episource/picopdio/schematics/picopdio.kicad_sch

## KiCad design schematics/picopdio.kicad_sch (2023-12-19)

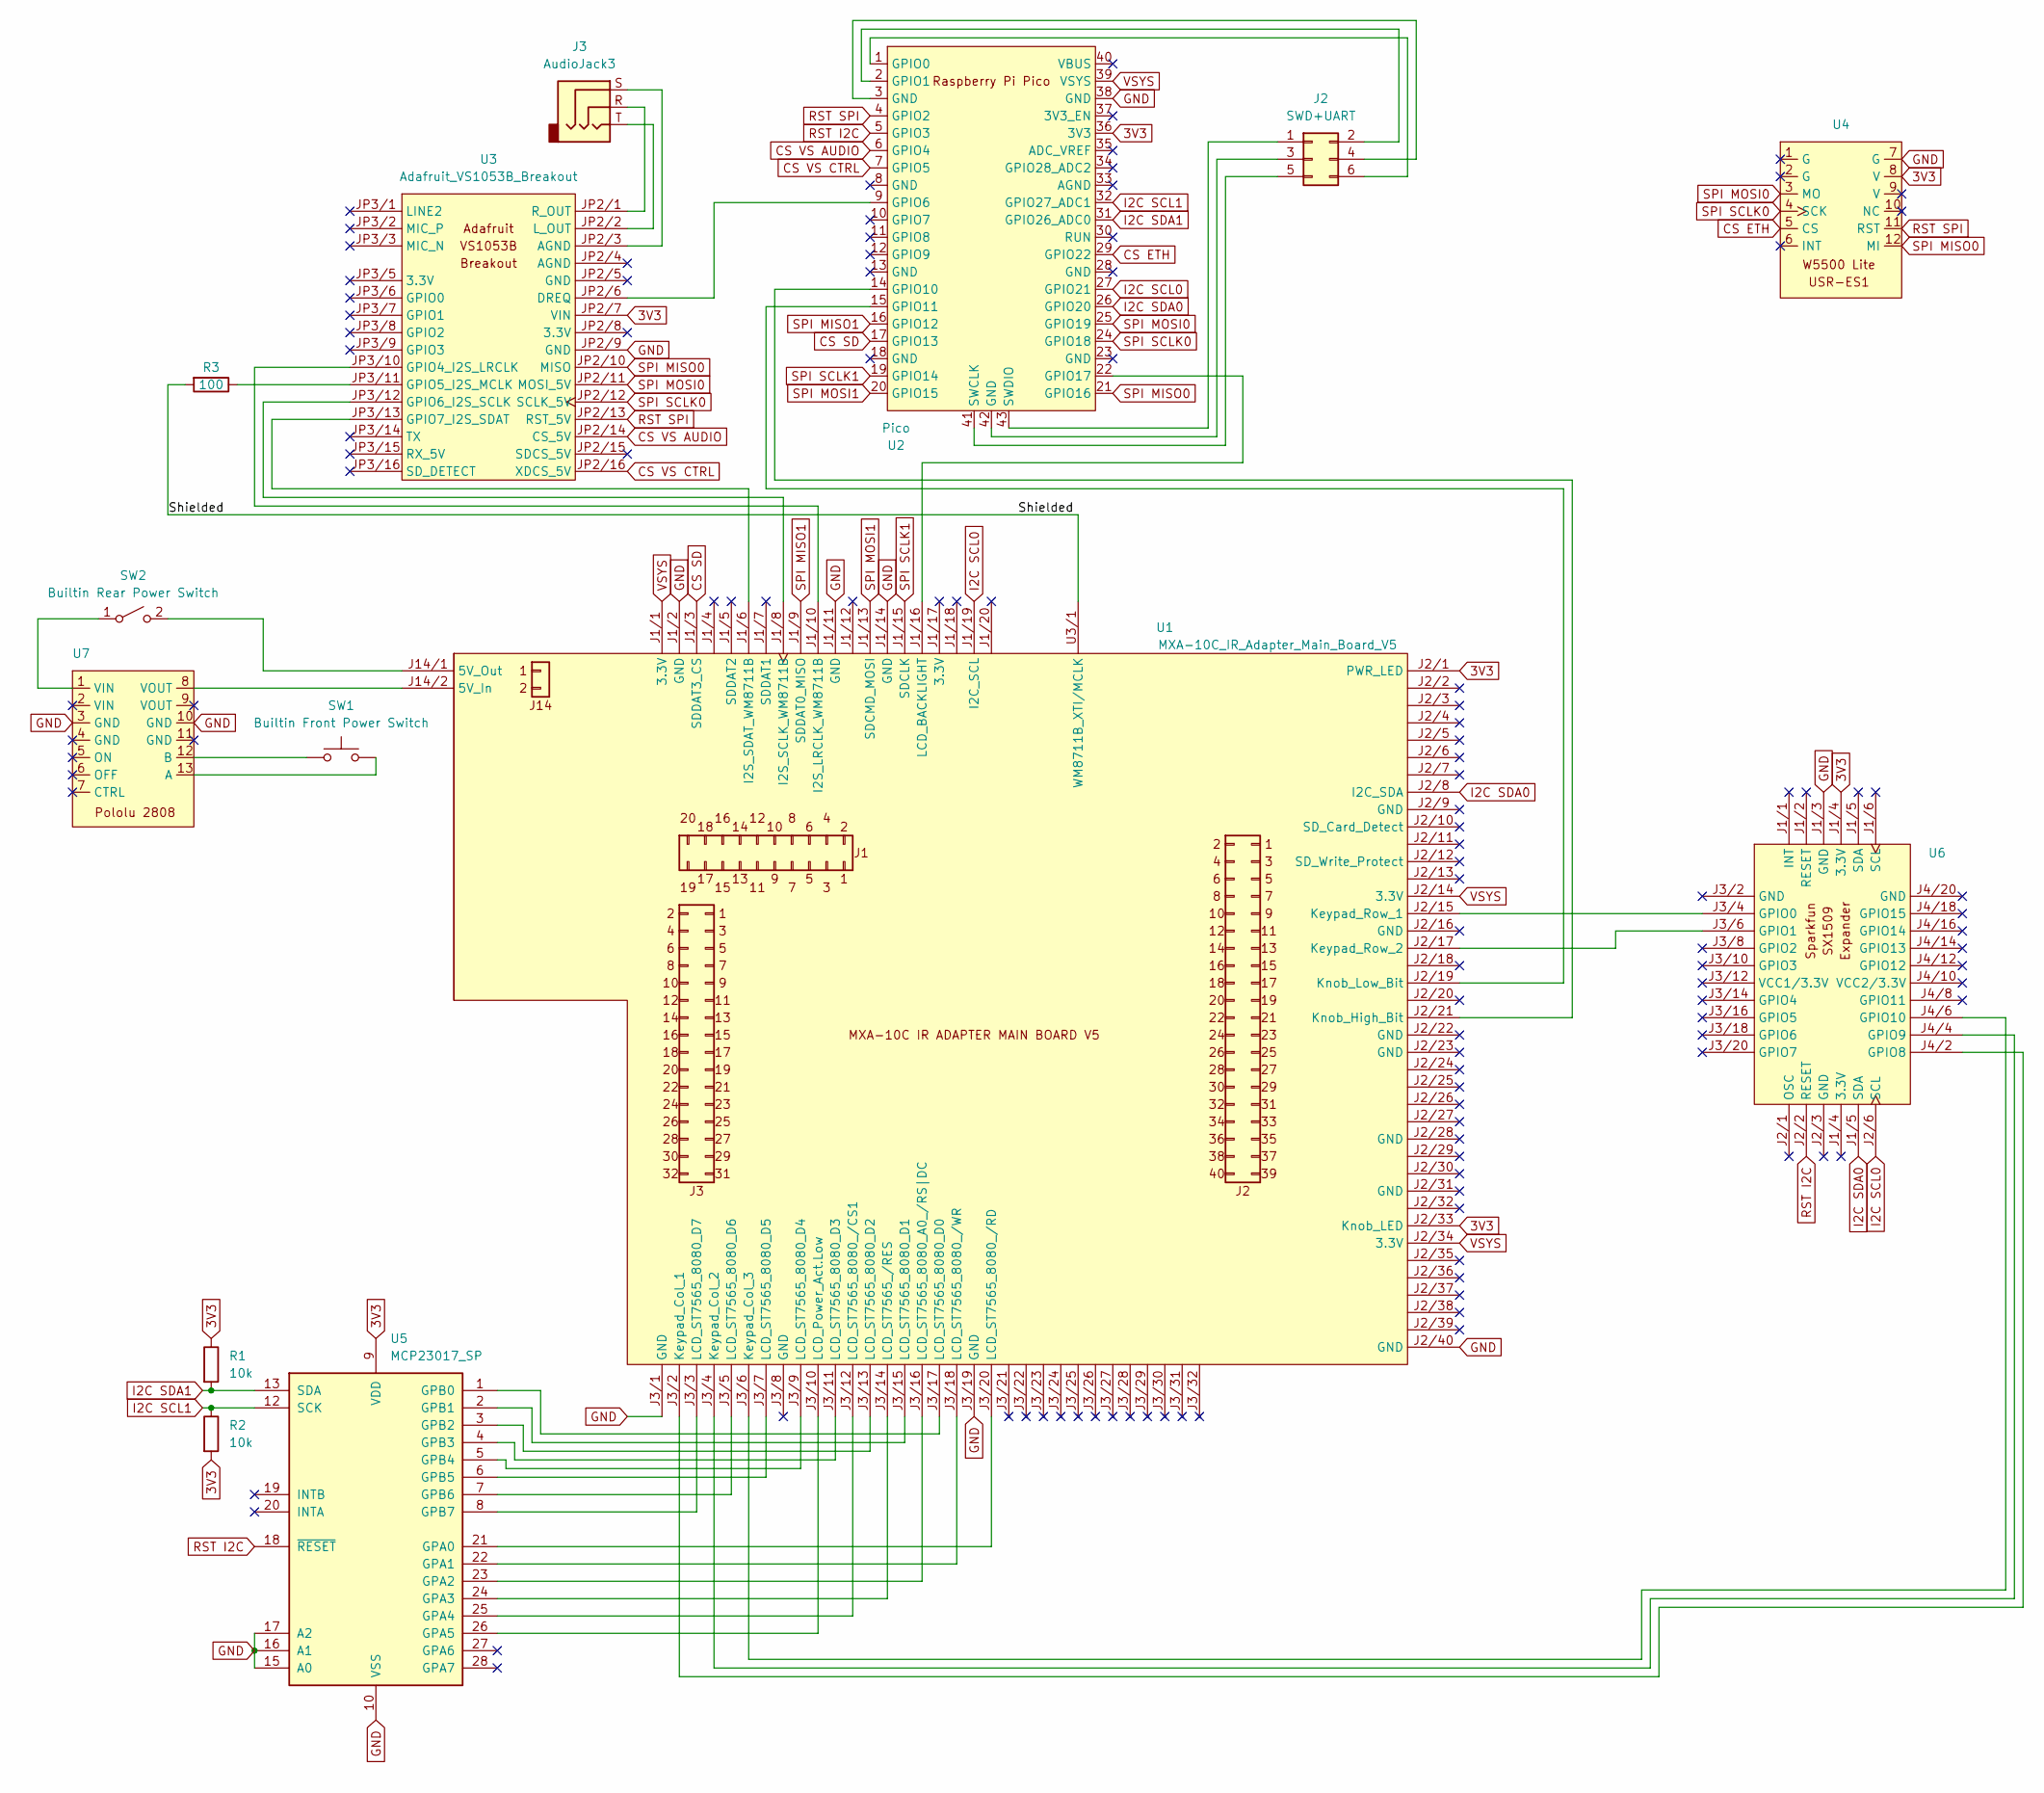
[picture p2: schematic picopdio.kicad_sch]

Parts:
J2: SWD+UART
J3: AudioJack3
R1, R2: 10k
R3: 100
SW1: Builtin Front Power Switch
SW2: Builtin Rear Power Switch
U1: MXA-10C_IR_Adapter_Main_Board_V5
U2: Pico
U3: Adafruit_VS1053B_Breakout
U4: W5500_Lite USR-ES1
U5: MCP23017_SP; DIP-28_W7.62mm
U6: SparkFun_SX1509_Expander
U7: Pololu_2808

Connections:
3V3: R1.1, R2.2, U1.J2/1 (PWR_LED), U1.J2/33 (Knob_LED), U2.36 (3V3), U3.JP2/7 (VIN), U4.8 (V), U5.9 (VDD), U6.J1/4 (3.3V)
CS ETH: U2.29 (GPIO22), U4.5 (CS)
CS SD: U1.J1/3 (SDDAT3_CS), U2.17 (GPIO13)
CS VS AUDIO: U2.6 (GPIO4), U3.JP2/14 (CS_5V)
CS VS CTRL: U2.7 (GPIO5), U3.JP2/16 (XDCS_5V)
GND: U1.J1/2 (GND), U1.J1/11 (GND), U1.J1/14 (GND), U1.J2/40 (GND), U1.J3/1 (GND), U1.J3/19 (GND), U2.38 (GND), U3.JP2/9 (GND), U4.7 (G), U5.10 (VSS), U5.15 (A0), U5.16 (A1), U5.17 (A2), U6.J1/3 (GND), U7.3 (GND), U7.10 (GND)
I2C SCL0: U1.J1/19 (I2C_SCL), U2.27 (GPIO21), U6.J2/6 (SCL)
I2C SCL1: R2.1, U2.32 (GPIO27_ADC1), U5.12 (SCK)
I2C SDA0: U1.J2/8 (I2C_SDA), U2.26 (GPIO20), U6.J1/5 (SDA)
I2C SDA1: R1.2, U2.31 (GPIO26_ADC0), U5.13 (SDA)
unnamed: J2.1, U2.43 (SWDIO)
unnamed: J2.2, U2.2 (GPIO1)
unnamed: J2.3, U2.42 (GND)
unnamed: J2.4, U2.3 (GND)
unnamed: J2.5, U2.41 (SWCLK)
unnamed: J2.6, U2.1 (GPIO0)
unnamed: J3.R, U3.JP2/1 (R_OUT)
unnamed: J3.S, U3.JP2/3 (AGND)
unnamed: J3.T, U3.JP2/2 (L_OUT)
unnamed: R3.1, U3.JP3/11 (GPIO5_I2S_MCLK)
unnamed: SW1.1, U7.12 (B)
unnamed: SW1.2, U7.13 (A)
unnamed: SW2.1 (A), U7.1 (VIN)
unnamed: SW2.2 (B), U1.J14/1 (5V_Out)
unnamed: U1.J1/6 (I2S_SDAT_WM8711B), U3.JP3/13 (GPIO7_I2S_SDAT)
unnamed: U1.J1/8 (I2S_SCLK_WM8711B), U3.JP3/12 (GPIO6_I2S_SCLK)
unnamed: U1.J1/10 (I2S_LRCLK_WM8711B), U3.JP3/10 (GPIO4_I2S_LRCLK)
unnamed: U1.J1/16 (LCD_BACKLIGHT), U2.22 (GPIO17)
unnamed: U1.J2/15 (Keypad_Row_1), U6.J3/4 (GPIO0)
unnamed: U1.J2/17 (Keypad_Row_2), U6.J3/6 (GPIO1)
unnamed: U1.J2/19 (Knob_Low_Bit), U2.15 (GPIO11)
unnamed: U1.J2/21 (Knob_High_Bit), U2.14 (GPIO10)
unnamed: U1.J3/2 (Keypad_Col_1), U6.J4/2 (GPIO8)
unnamed: U1.J3/3 (LCD_ST7565_8080_D7), U5.8 (GPB7)
unnamed: U1.J3/4 (Keypad_Col_2), U6.J4/4 (GPIO9)
unnamed: U1.J3/5 (LCD_ST7565_8080_D6), U5.7 (GPB6)
unnamed: U1.J3/6 (Keypad_Col_3), U6.J4/6 (GPIO10)
unnamed: U1.J3/7 (LCD_ST7565_8080_D5), U5.6 (GPB5)
unnamed: U1.J3/9 (LCD_ST7565_8080_D4), U5.5 (GPB4)
unnamed: U1.J3/10 (LCD_Power_Act.Low), U5.26 (GPA5)
unnamed: U1.J3/11 (LCD_ST7565_8080_D3), U5.4 (GPB3)
unnamed: U1.J3/12 (LCD_ST7565_8080_/CS1), U5.25 (GPA4)
unnamed: U1.J3/13 (LCD_ST7565_8080_D2), U5.3 (GPB2)
unnamed: U1.J3/14 (LCD_ST7565_/RES), U5.24 (GPA3)
unnamed: U1.J3/15 (LCD_ST7565_8080_D1), U5.2 (GPB1)
unnamed: U1.J3/16 (LCD_ST7565_8080_A0_/RS|DC), U5.23 (GPA2)
unnamed: U1.J3/17 (LCD_ST7565_8080_D0), U5.1 (GPB0)
unnamed: U1.J3/18 (LCD_ST7565_8080_/WR), U5.22 (GPA1)
unnamed: U1.J3/20 (LCD_ST7565_8080_/RD), U5.21 (GPA0)
unnamed: U1.J14/2 (5V_In), U7.8 (VOUT)
unnamed: U2.9 (GPIO6), U3.JP2/6 (DREQ)
RST I2C: U2.5 (GPIO3), U5.18 (~RESET), U6.J2/2 (RESET)
RST SPI: U2.4 (GPIO2), U3.JP2/13 (RST_5V), U4.11 (RST)
SPI MISO0: U2.21 (GPIO16), U3.JP2/10 (MISO), U4.12 (MI)
SPI MISO1: U1.J1/9 (SDDAT0_MISO), U2.16 (GPIO12)
SPI MOSI0: U2.25 (GPIO19), U3.JP2/11 (MOSI_5V), U4.3 (MO)
SPI MOSI1: U1.J1/13 (SDCMD_MOSI), U2.20 (GPIO15)
SPI SCLK0: U2.24 (GPIO18), U3.JP2/12 (SCLK_5V), U4.4 (SCK)
SPI SCLK1: U1.J1/15 (SDCLK), U2.19 (GPIO14)
Shielded: R3.2, U1.U3/1 (WM8711B_XTI/MCLK)
VSYS: U1.J1/1 (3.3V), U1.J2/14 (3.3V), U1.J2/34 (3.3V), U2.39 (VSYS)
